ra0sms/sequenser/code/User/ch32v00x_it.c

/********************************** (C) COPYRIGHT *******************************
 * File Name          : ch32v00x_it.c
 * Author             : WCH
 * Version            : V1.0.0
 * Date               : 2023/12/25
 * Description        : Main Interrupt Service Routines.
*********************************************************************************
* Copyright (c) 2021 Nanjing Qinheng Microelectronics Co., Ltd.
* Attention: This software (modified or not) and binary are used for 
* microcontroller manufactured by Nanjing Qinheng Microelectronics.
*******************************************************************************/
#include <ch32v00x_it.h>

void NMI_Handler(void) __attribute__((interrupt("WCH-Interrupt-fast")));
void HardFault_Handler(void) __attribute__((interrupt("WCH-Interrupt-fast")));

/*********************************************************************
 * @fn      NMI_Handler
 *
 * @brief   This function handles NMI exception.
 *
 * @return  none
 */
void NMI_Handler(void)
{
  while (1)
  {
  }
}

/*********************************************************************
 * @fn      HardFault_Handler
 *
 * @brief   This function handles Hard Fault exception.
 *
 * @return  none
 */
void HardFault_Handler(void)
{
  while (1)
  {
  }
}

__attribute__((interrupt("WCH-Interrupt-fast")))
void TIM2_IRQHandler(void)
{
    static u8 j = 0;
    if (TIM_GetITStatus(TIM2, TIM_IT_Update) == SET)
    {
        TIM_ClearITPendingBit(TIM2, TIM_IT_Update);
        GPIO_WriteBit(GPIOC, GPIO_Pin_7, (j == 0) ? (j = Bit_SET) : (j = Bit_RESET));
    }
}
